bartkepl/CanGeigerProbe/sim/HV_flyback.asc

B1: bv; V=if( V(hv)<400, if( time-20u*floor(time/20u) < 7u, 5, 0 ), 0 )
C1: cap; 10n
C2: cap; 2.2n; V=1k
D1: diode; BAV21WS
D2: diode; STTH112
L1: ind; 75�; Rser=1m
L2: ind; 67.5m; Rser=1m
M1: nmos; DMN3404L
R1: res; 100k
R2: res; 22
R3: res; 2.2
R4: res; 100
R5: res; 500Meg
R6: res; 500Meg
R7: res; 1Meg
V1: voltage; 5
Named nets: 0, hv
.model DMN3404L VDMOS(Vto=0.9 Kp=18 Rd=25m Rs=5m Rg=3 Vds=30

+ Cgs=400p Cgdmax=150p Cgdmin=15p Cjo=50p mfg=Diodes)
K1  L1 L2 0.994
.model BAV21WS D(Is=2n Rs=2 N=1.9 Cjo=1.5p Vj=0.75 M=0.33 BV=250 Ibv=10u tt=30n)
.model STTH112 D(Is=4n Rs=1.5 N=2 Cjo=8p Vj=0.8 M=0.45 BV=1200 Ibv=10u tt=25n)
.tran 10m
